emeb/g081_audio/Firmware/common/shared_i2c.h

/*
 * shared_i2c.h - shared I2C bus basic routines
 * 07-12-19 E. Brombaugh
 */

#ifndef __shared_i2c__
#define __shared_i2c__

#ifdef __cplusplus
extern "C" {
#endif

#include "main.h"

extern I2C_HandleTypeDef hi2c2;

void shared_i2c_init(void);
void shared_i2c_reset(void);

#ifdef __cplusplus
}
#endif

#endif
