emeb/g081_audio/Firmware/mv_comp/mv_names.h

/*
 * mv_names.h
 * names of Midiverb Programs
 */

const char *mv_prog_names[63] =
{
	"0.2 S Br",		// 1
	"0.2 S Wm",		// 2
	"0.2 M Br",		// 3
	"0.3 S Br",		// 4
	"0.3 S Ww",		// 5
	"0.4 M Br",		// 6
	"0.4 M Wm",		// 7
	"0.6 S Br",		// 8
	"0.6 M Wm",		// 9
	"0.6 M Dk",		// 10
	"0.8 S Br",		// 11
	"0.8 L Wm",		// 12
	"1.0 S Ww",		// 13
	"1.0 M Ww",		// 14
	"1.0 L Br",		// 15
	"1.2 M Wm",		// 16
	"1.2 S Wm",		// 17
	"1.2 S Br",		// 18
	"1.4 L Wm",		// 19
	"1.4 L Dk",		// 20
	"1.4 M Wm",		// 21
	"1.6 S Dk",		// 22
	"1.6 L Br",		// 23
	"1.6 M Br",		// 24
	"1.8 L Dk",		// 25
	"1.8 L Br",		// 26
	"1.8 M Wm",		// 27
	"2.0 L Br",		// 28
	"2.0 M Wm",		// 29
	"2.0 L Wm",		// 30
	"2.5 M Wm",		// 31
	"2.5 L Br",		// 32
	"2.5 M Dk",		// 33
	"2.8 S Br",		// 34
	"2.8 M Br",		// 35
	"3.0 L Br",		// 36
	"3.0 L Wm",		// 37
	"3.0 M Dk",		// 38
	"3.5 L Br",		// 39
	"3.5 M Wm",		// 40
	"4.0 M Dk",		// 41
	"4.0 M Br",		// 42
	" 5  L Wm",		// 43
	" 8  L Br",		// 44
	" 8  L Wm",		// 45
	"10  L Br",		// 46
	"10  L Wm",		// 47
	"16  L Dk",		// 48
	"18  X Br",		// 49
	"20  X Dk",		// 50
	"Gate 100",		// 51
	"Gate 150",		// 52
	"Gate 200",		// 53
	"Gate 250",		// 54
	"Gate 300",		// 55
	"Gate 350",		// 56
	"Gate 400",		// 57
	"Gate 500",		// 58
	"Gate 600",		// 59
	"Revs 300",		// 60
	"Revs 400",		// 61
	"Revs 500",		// 62
	"Revs 600",		// 63
};
